Dieu-de-l-elec/RGB_connect/Firmware/Blynk IoT app RGB Connect.jpg

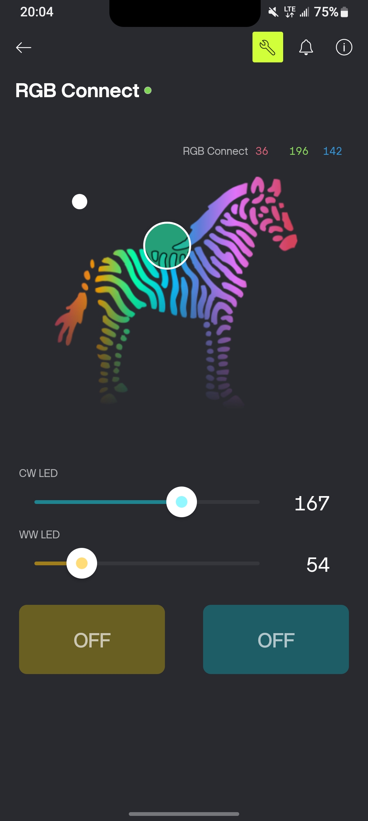
Firmware/Blynk IoT app RGB Connect.jpg
