Dieu-de-l-elec/RGB_connect/Firmware/RGB CONNECT Blynk dashboard.png

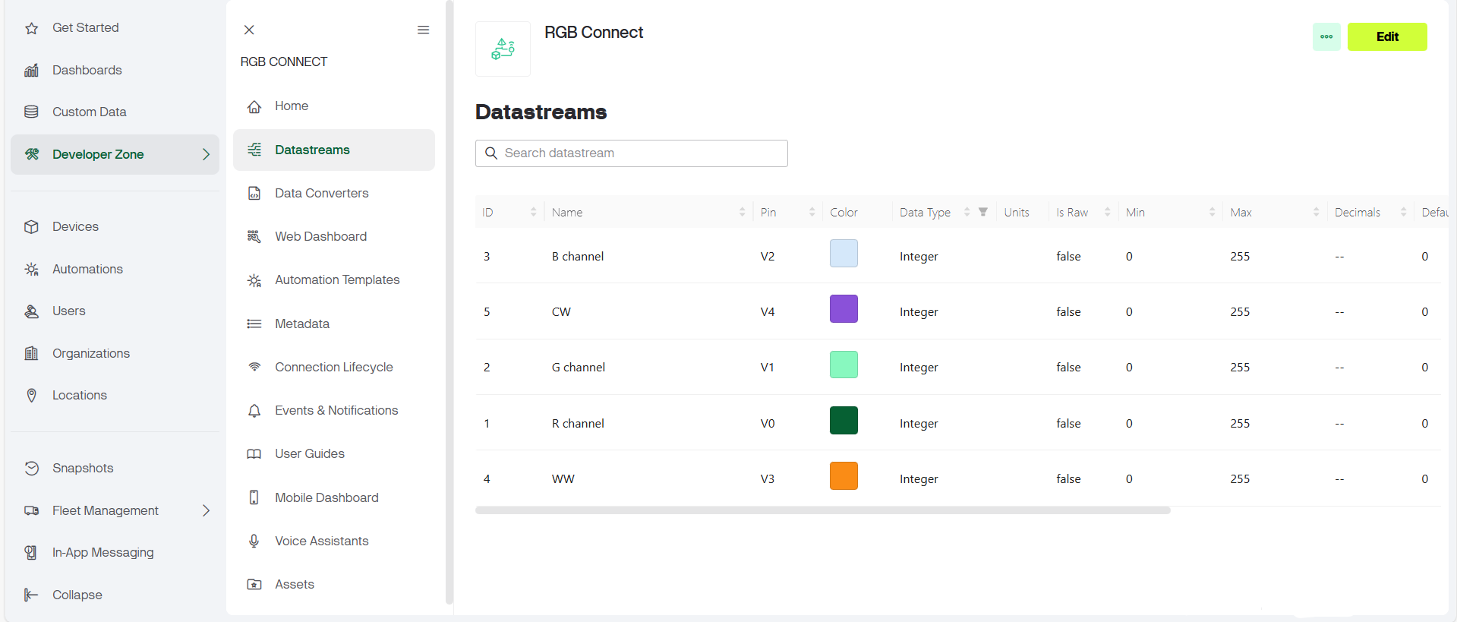
Firmware/RGB CONNECT Blynk dashboard.png
