Dieu-de-l-elec/RGB_connect/PCB/PCB LAYOUT 2.png

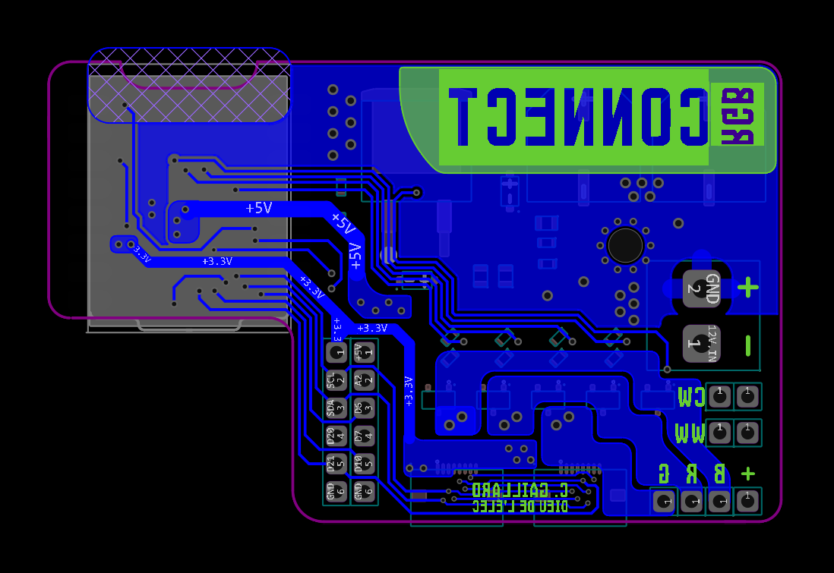
PCB/PCB LAYOUT 2.png
