Dieu-de-l-elec/RGB_connect/PCB/PCB LAYOUT 3.png

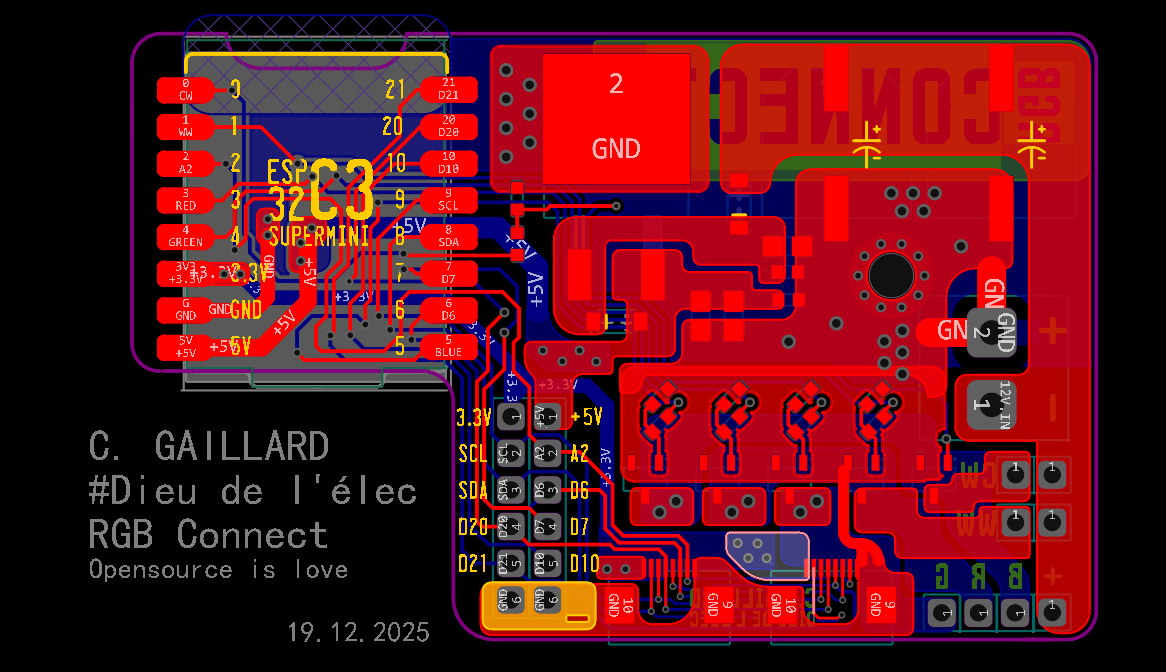
PCB/PCB LAYOUT 3.png
