Dieu-de-l-elec/RGB_connect/RENDERS/PCB 3d Model EASYEDA Viewer Bottom.png

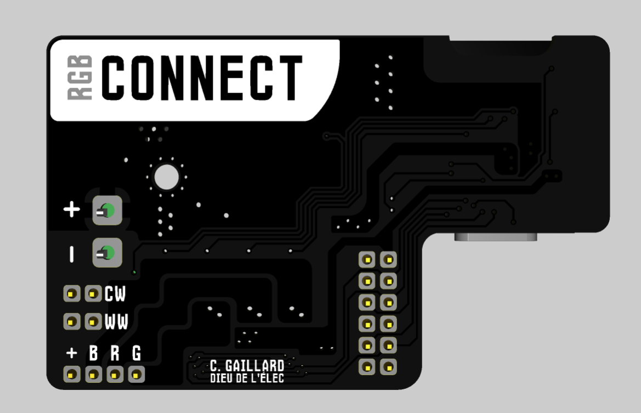
RENDERS/PCB 3d Model EASYEDA Viewer Bottom.png
