Dieu-de-l-elec/RGB_connect/RENDERS/PCB 3d Model EASYEDA Viewer iso.png

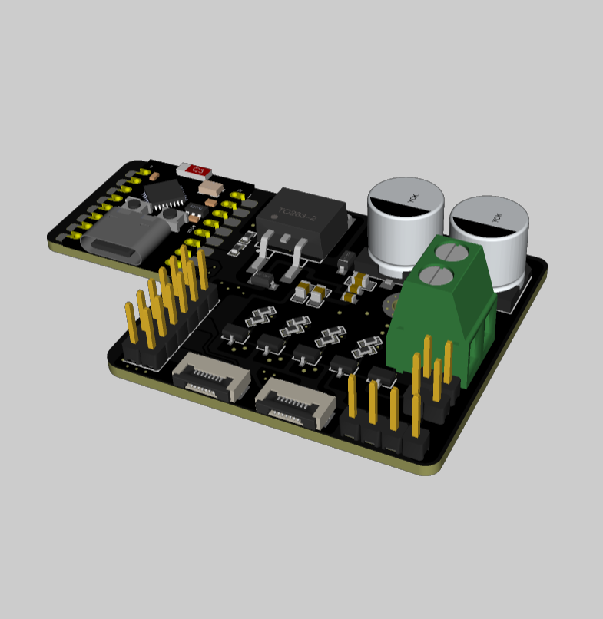
RENDERS/PCB 3d Model EASYEDA Viewer iso.png
