Dieu-de-l-elec/RGB_connect/RENDERS/PCB RENDER 01.png

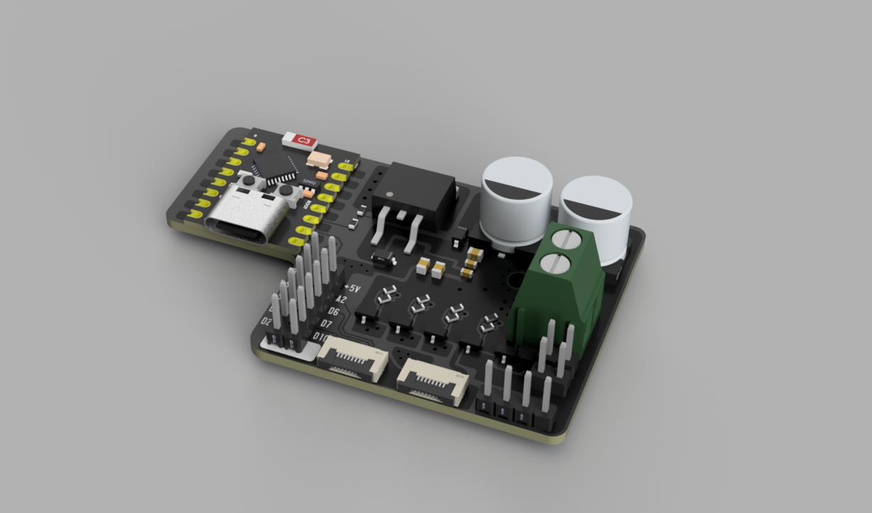
RENDERS/PCB RENDER 01.png
