Dieu-de-l-elec/RGB_connect/RENDERS/PCB RENDER 02.png

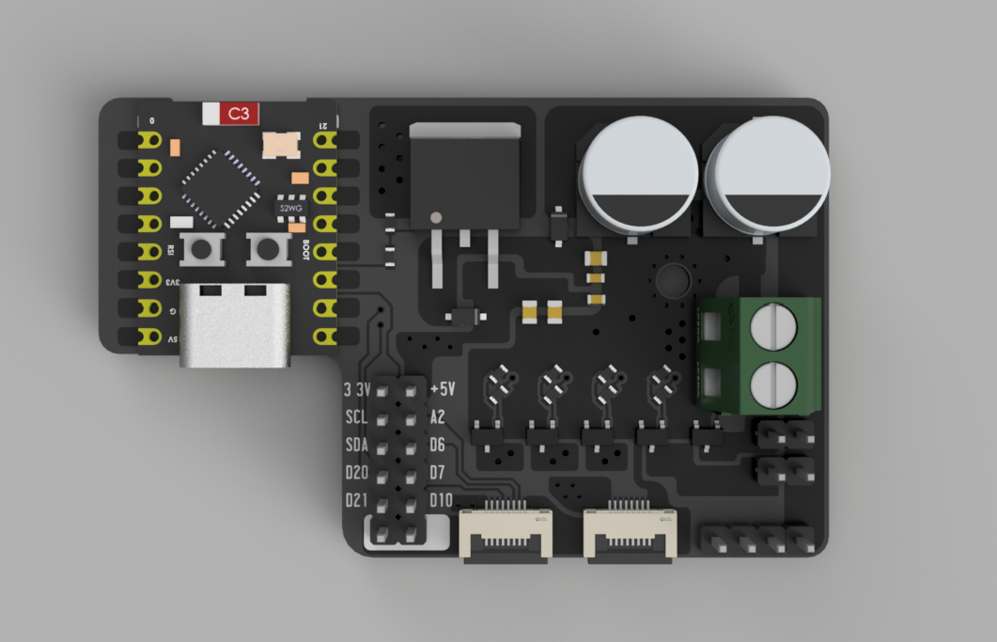
RENDERS/PCB RENDER 02.png
