Dieu-de-l-elec/RGB_connect/RENDERS/PCB RENDER 03.png

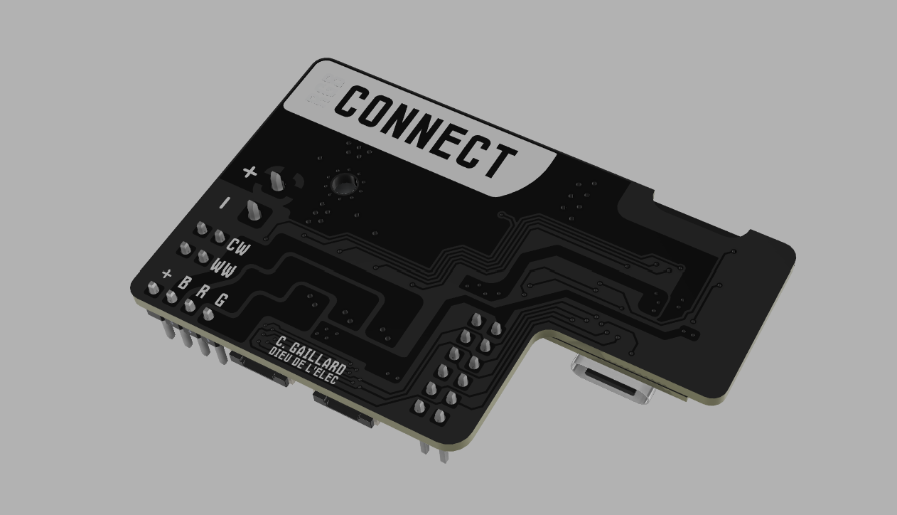
RENDERS/PCB RENDER 03.png
