Dieu-de-l-elec/RGB_connect/RENDERS/PCB RENDER 04.png

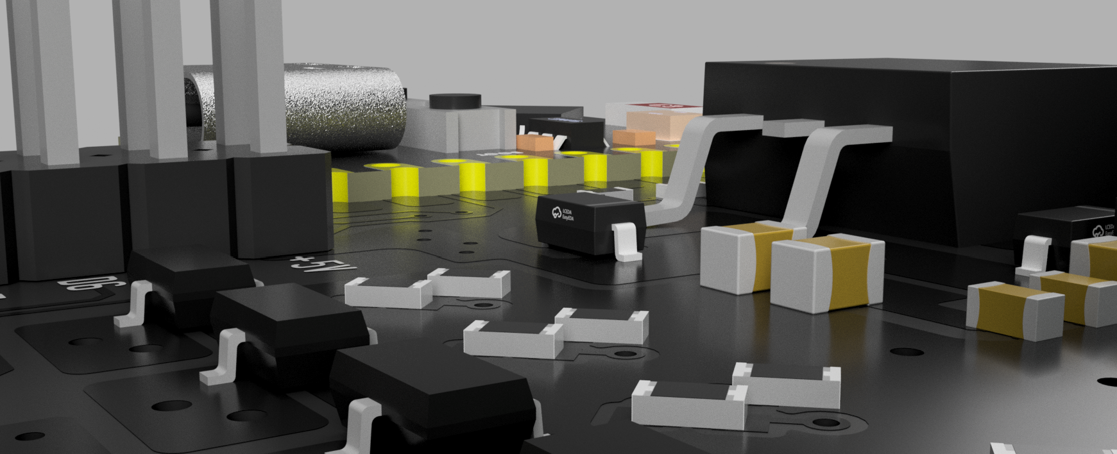
RENDERS/PCB RENDER 04.png
