Dieu-de-l-elec/RGB_connect/RENDERS/RGB CONNECT FINAL RENDERS 06.png

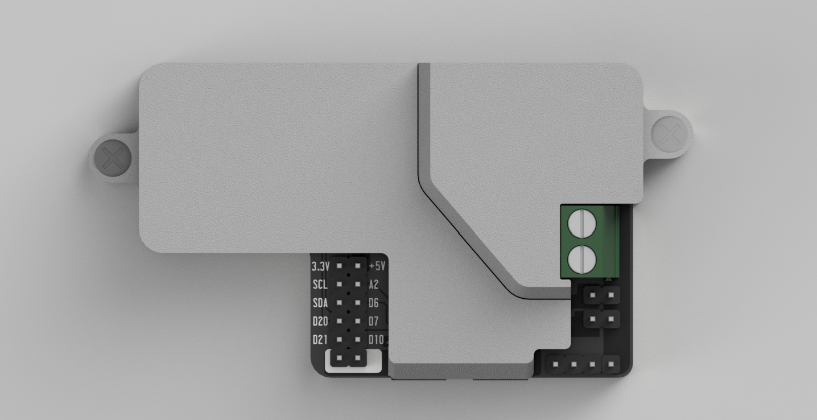
RENDERS/RGB CONNECT FINAL RENDERS 06.png
