Dieu-de-l-elec/RGB_connect/BUILD/build01.jpg

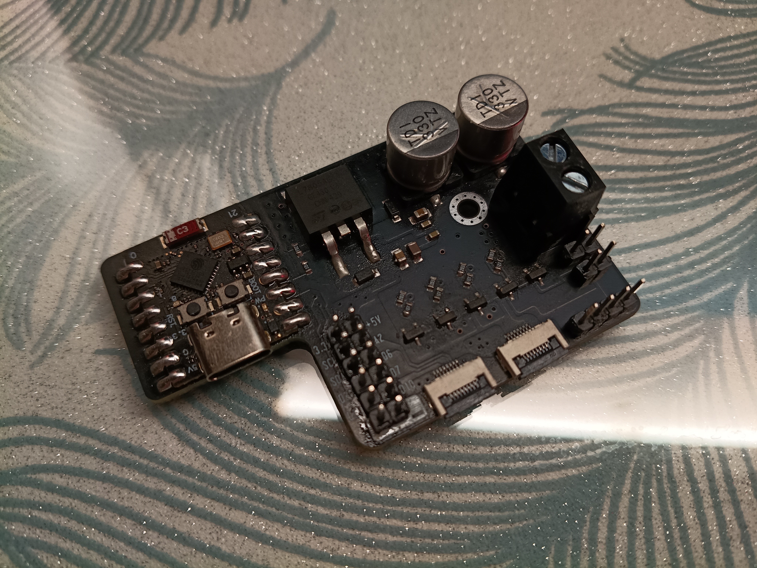
BUILD/build01.jpg
