Dieu-de-l-elec/RGB_connect/BUILD/build03.jpg

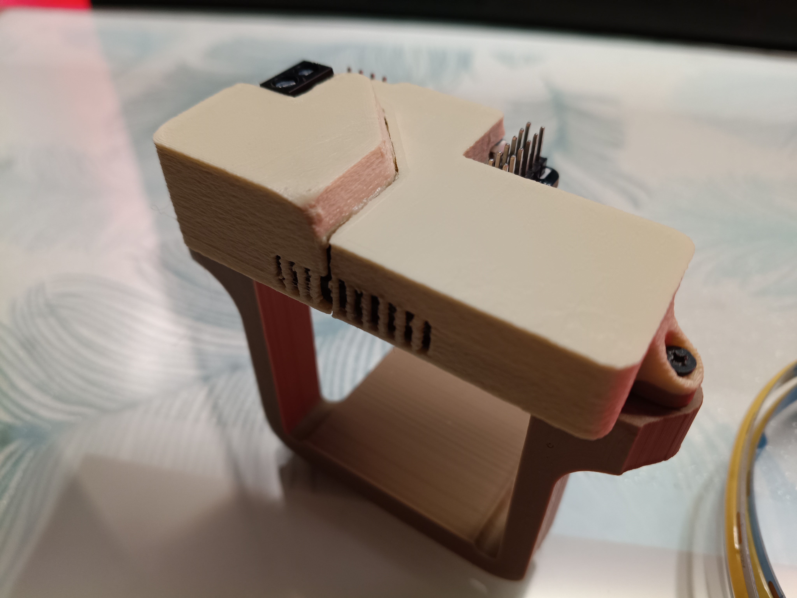
BUILD/build03.jpg
