Dieu-de-l-elec/RGB_connect/BUILD/build04.jpg

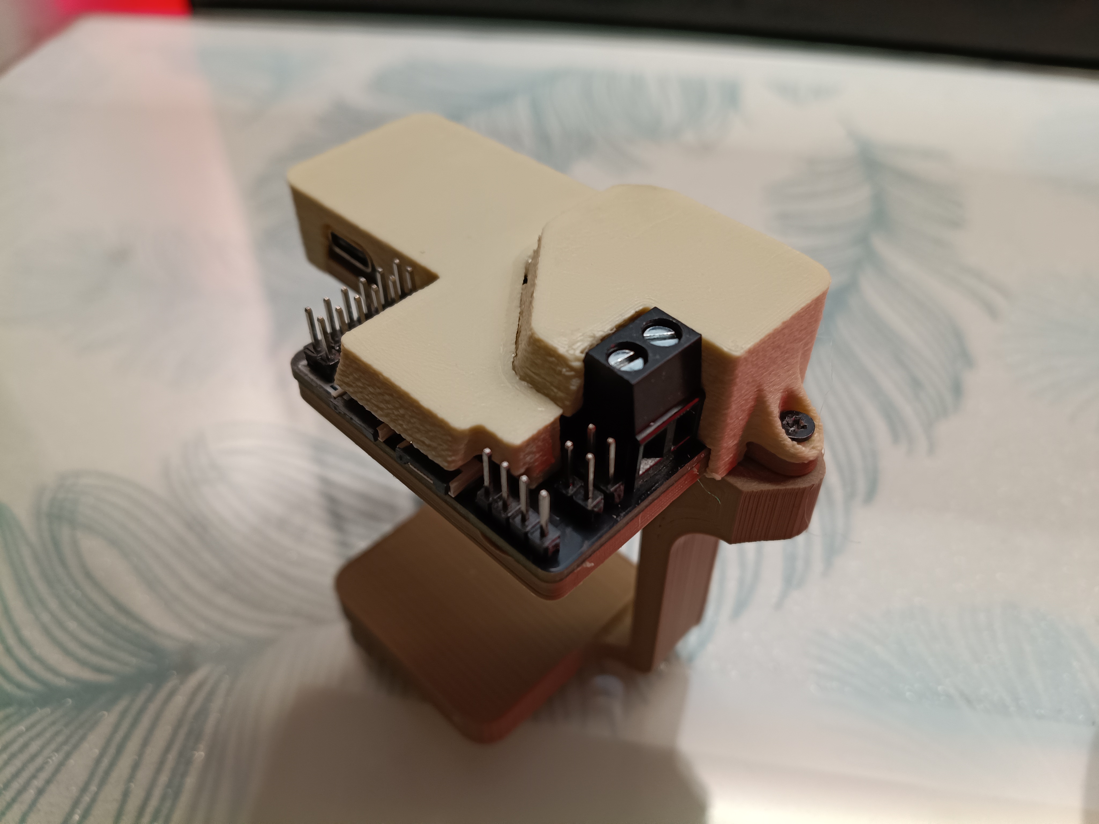
BUILD/build04.jpg
