Dieu-de-l-elec/RGB_connect/BUILD/build05.jpg

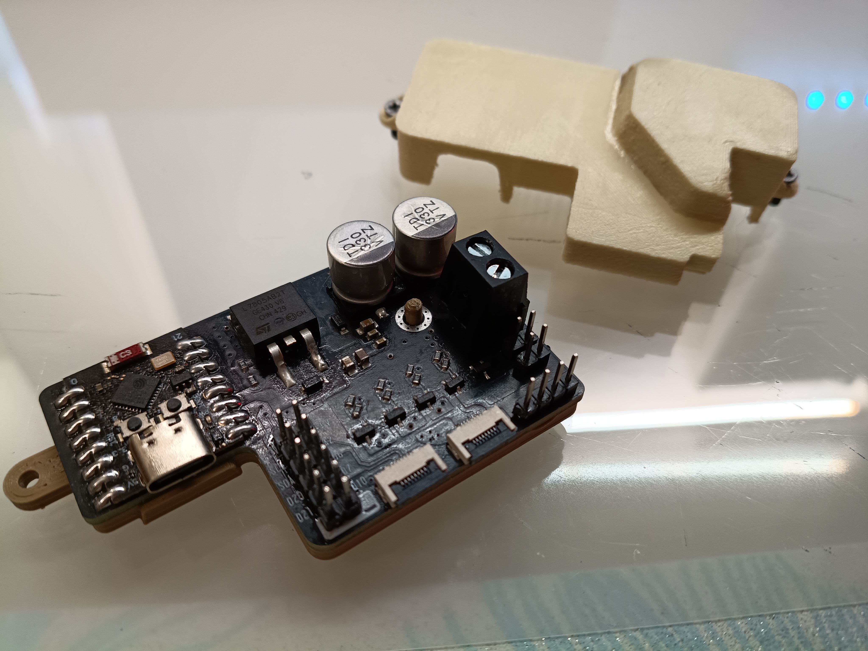
BUILD/build05.jpg
